SuperTails/ipotcas/rustplot/plotters-doc-data/0.png

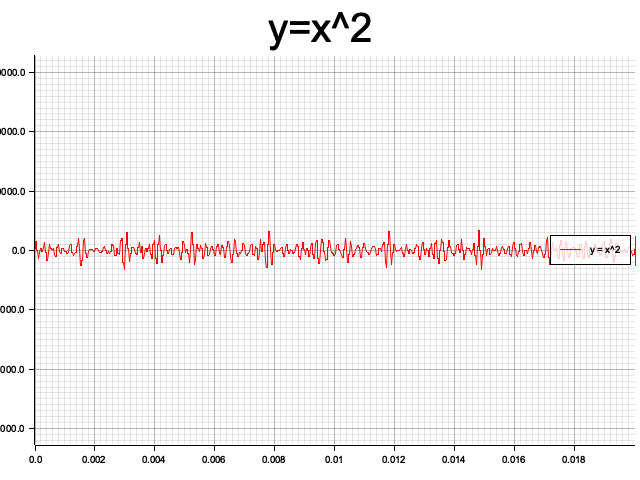
rustplot/plotters-doc-data/0.png
