SuperTails/ipotcas/Core/Inc/modulation.h

#pragma once
#include <stdint.h>

#define TX_RAW_STREAM 0

#define MODULATION_ASK 0
#define MODULATION_QAM 1

#if MODULATION_ASK

#define AGC 0
#define AVG_PHASE_CORRECTION 0
#define PHASE_CORRECTION 1
#define TRAINING_PHASE 1.5707f
#define BITS_PER_SYMBOL 2
#define SYMBOL_PERIOD_US 8000

// end MODULATION_ASK
#elif MODULATION_QAM 

#define AGC 1
#define AVG_PHASE_CORRECTION 1
#define PHASE_CORRECTION 1
#define TRAINING_PHASE 0.0f
#define SYMBOL_PERIOD_US 4000

#define TRELLIS_CODING 1

#if TRELLIS_CODING
#define BITS_PER_SYMBOL 4
#else
#define BITS_PER_SYMBOL 5
#endif

// end MODULATION_QAM
#else
#error "Must choose a modulation scheme"
#endif

#if 1
#define HAMMING_BLOCK_SIZE 15
#define HAMMING_MESSAGE_SIZE 11
#define HAMMING_ENCODE hamming_encode_15_11
#define HAMMING_DECODE hamming_decode_15_11
#elif 0
#define HAMMING_BLOCK_SIZE 7
#define HAMMING_MESSAGE_SIZE 4
#define HAMMING_ENCODE hamming_encode_7_4
#define HAMMING_DECODE hamming_decode_7_4
#elif 0
#define HAMMING_BLOCK_SIZE 8
#define HAMMING_MESSAGE_SIZE 8
#define HAMMING_ENCODE hamming_encode_nop
#define HAMMING_DECODE hamming_decode_nop
#else
#error "Must choose a hamming code"
#endif

// 1 / (48 kHz) == 62500 ns / 3
#define SAMPLE_PERIOD_NS_NUM 62500
#define SAMPLE_PERIOD_NS_DEN 3

#define SAMPLE_PERIOD_NS (SAMPLE_PERIOD_NS_NUM / SAMPLE_PERIOD_NS_DEN) 

#define SAMPLE_RATE_HZ 48000

#define CARRIERS 16

static const int CARRIER_FREQUENCIES_HZ[CARRIERS] = {
 6500,
  7000,
  7500,
   8000,
   8500,
   9000,
   9500,
  10000,
  10500,
  11000,
  11500,
  12000,
  12500,
  13000,
  14000,
  14500,
};

static const int CARRIER_PERIODS_NS[CARRIERS] = {
  //1000000, // 1 kHz
  //666666, // 1.5 kHz
  //500000, // 2.0 kHz
  //400000, // 2.5 kHz
  //333333, // 3 kHz
  //285714, // 3.5 kHz (GOOD)

  /*250000, // 4 kHz
  222222, // 4.5 kHz
  200000, // 5 kHz
  181818, // 5.5 kHz (AWFUL??)
  166666, // 6 kHz
  153846, // 6.5 kHz
  142857, // 7 kHz
  133333, // 7.5 kHz*/
  125000, // 8 kHz
  117647, // 8.5 kHz
  111111, // 9 kHz
  105263, // 9.5 kHz
  100000, // 10 kHz
  95238, // 10.5 kHz
  90909, // 11 kHz
  86957, // 11.5 kHz
  83333, // 12 kHz
  80000, // 12.5 kHz
  76923, // 13 kHz
  74074, // 13.5 kHz
};

//#define CARRIER_PERIOD_NS 250000 // 4khz
//#define CARRIER_PERIOD_NS 166666 // 6khz
//#define CARRIER_FREQUENCY (1.0e9 / CARRIER_PERIOD_NS)

#define SYMBOL_GAP_US (4 * SYMBOL_PERIOD_US)
#define TRAIN_PERIOD_US (2 * SYMBOL_PERIOD_US)

#define SAMPLES_PER_SYMBOL ((SAMPLE_RATE_HZ / 1000) * (SYMBOL_PERIOD_US / 1000))


static const int8_t CONSTELLATION_TO_SYMBOL[9][9] = {
  { -1, -1, -1, 28, -1, 27, -1, -1, -1 },
  { -1, -1, 14, -1, 1, -1, 12, -1, -1 },
  { -1, 16, -1, 23, -1, 17, -1, 22, -1 },
  { 7, -1, 9, -1, 6, -1, 11, -1, 4 },
  { -1, 25, -1, 30, -1, 26, -1, 29, -1 },
  { 0, -1, 15, -1, 2, -1, 13, -1, 3 },
  { -1, 18, -1, 21, -1, 19, -1, 20, -1 },
  { -1, -1, 8, -1, 5, -1, 10, -1, -1 },
  { -1, -1, -1, 31, -1, 24, -1, -1, -1 },
};

static const int8_t SYMBOL_TO_CONSTELLATION_I[] = { -4,  0, 0, 4,  4, 0,  0, -4, -2, -2, 2,  2,  2, 2, -2, -2, -3,  1, -3, 1, 3, -1,  3, -1, 1, -3, 1,  1, -1, 3, -1, -1 };
static const int8_t SYMBOL_TO_CONSTELLATION_Q[] = {  1, -3, 1, 1, -1, 3, -1, -1,  3, -1, 3, -1, -3, 1, -3,  1, -2, -2,  2, 2, 2,  2, -2, -2, 4,  0, 0, -4, -4, 0,  0,  4 };
